FMG9167/Mechanical-PicoBoard-W/images/Aug-15-2.png

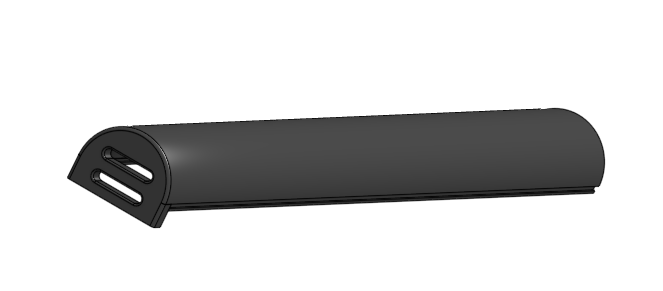
images/Aug-15-2.png
