FMG9167/Mechanical-PicoBoard-W/images/Aug-15-3.png

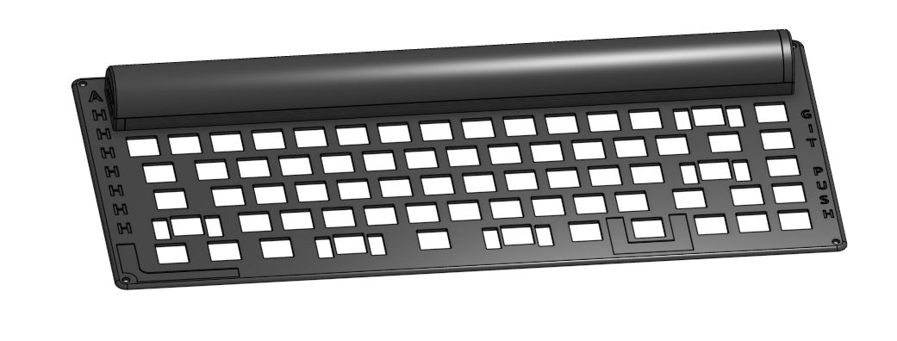
images/Aug-15-3.png
